curiouselectric/Lapse-O-Matic/Lapse-O-Matic_FIRMWARE/Lapse-O-Matic_SD_MMC/lapseomatic.h

#pragma once

#include <FS.h>
#include <esp_camera.h>
#include "config.h"

// This holds the various subroutines for the wifie camera to use
// This makes main code easier to read.

void switch_off_flash_LED();
void switch_on_flash_LED();
void flash_error(int my_flash_number);
void print_wakeup_reason();

void readFile(fs::FS &fs, const char * path,settings &my_settings_config);
void readSettings(fs::FS &fs, const char * path, settings &my_settings_config);

void configure_camera(camera_config_t &my_config, settings &my_settings_config);
